Nevada317/hpwm/src/main.c

#include "libs.h"
void loop();

// static uint8_t UserIn = 0;

int main(void) {
	EEPROM_Init();
	GPIO_Init();
	PWM_Init();
	ADC_Init();
	SYSTIMER_Init();
	MODES_Init();

	sei();

	while (1)
		loop();
}

void loop() {

}
