Nevada317/hpwm/src/libs.h

#ifndef LIBS_H_
#define LIBS_H_

// May be needed later:
#include <avr/eeprom.h>
#include <avr/io.h>
#include <avr/interrupt.h>
#include <avr/pgmspace.h>
// #include <avr/wdt.h>
// #include <util/delay.h>
// #include <util/crc16.h>
#include <util/delay.h>
#include <stdbool.h>
// #include <string.h>
#include <stdint.h>
// #include <stdio.h>
// #include <stdlib.h>


#include "gpio.h"
#include "pwm.h"
#include "modes.h"
#include "systimer.h"
#include "eeprom.h"
#include "adc.h"


#endif
